joaoandre26/SIE/Elevator_PCB/Imagens/bot.png

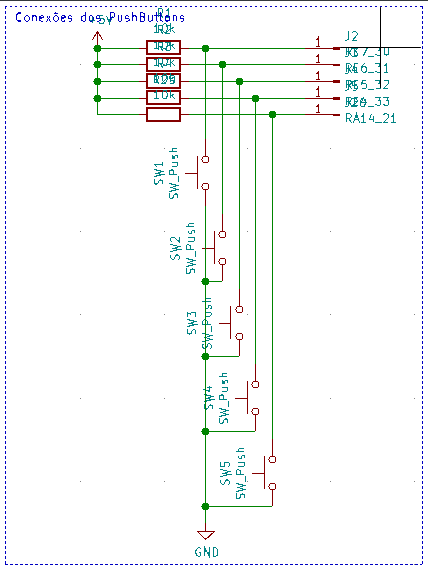
Elevator_PCB/Imagens/bot.png
