joaoandre26/SIE/Elevator_PCB/Imagens/fonte.png

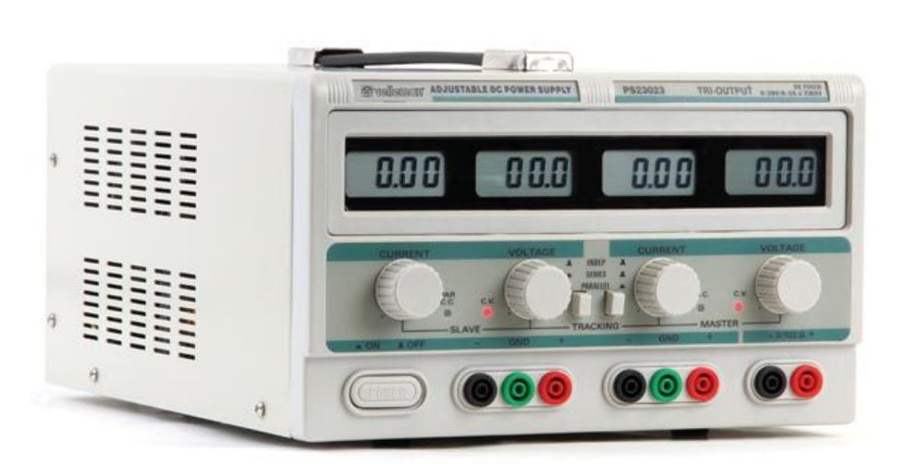
Elevator_PCB/Imagens/fonte.png
