joaoandre26/SIE/Elevator_PCB/Imagens/hall.png

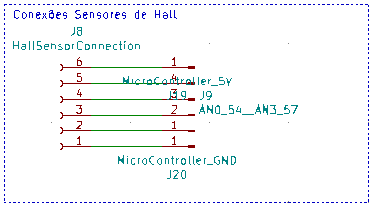
Elevator_PCB/Imagens/hall.png
