joaoandre26/SIE/Elevator_PCB/Imagens/sensores.png

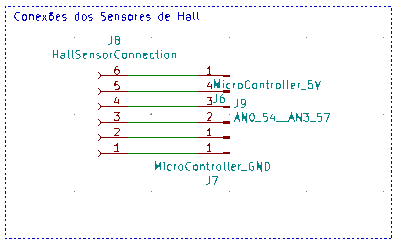
Elevator_PCB/Imagens/sensores.png
